AzatKaya1/KiCad-ESP32-S3-Custom-DevBoard/Images/RENDER3.png

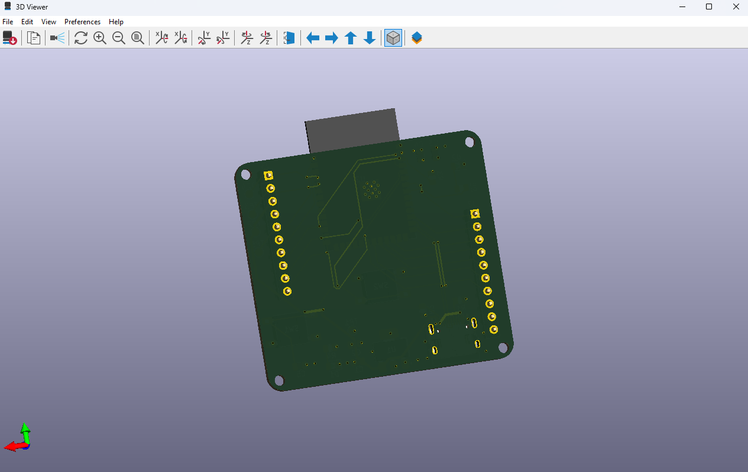
Images/RENDER3.png
